hayd1n/smart-desk-calendar/3D Models/Modules/E-Paper 7in5.SLDPRT

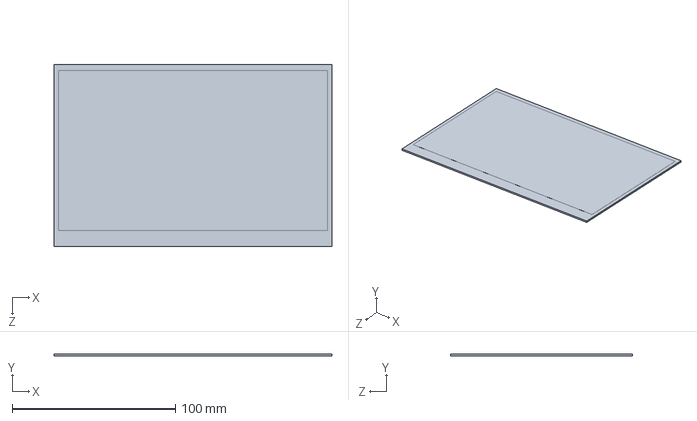
[picture p15: CAD file, 2023-11-22]
3D Models/Modules/E-Paper 7in5.SLDPRT
170.2 x 1.28 x 111.2 mm
